g7ltt/NQSMHS/55203_top_sm.png

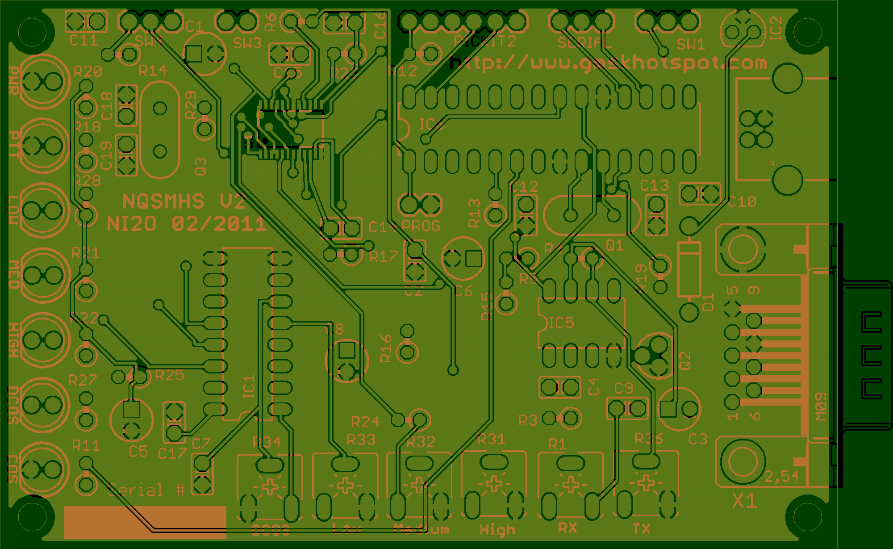
55203_top_sm.png
